csapidus/7971-dustoff-display/photos/IMG_0771.JPG

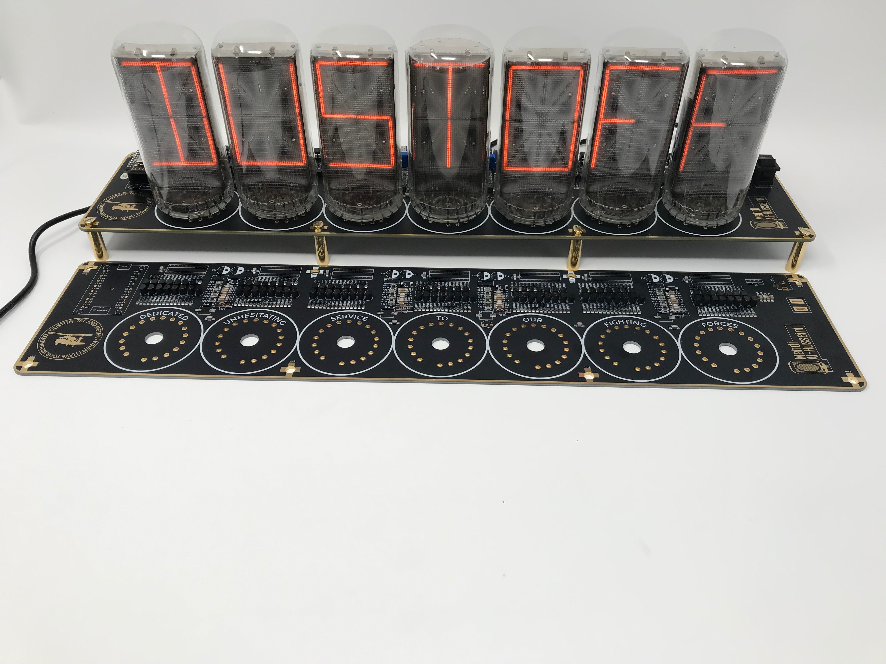
photos/IMG_0771.JPG
