csapidus/7971-dustoff-display/PCB/7971-MEDEVAC-F_SilkS.pdf

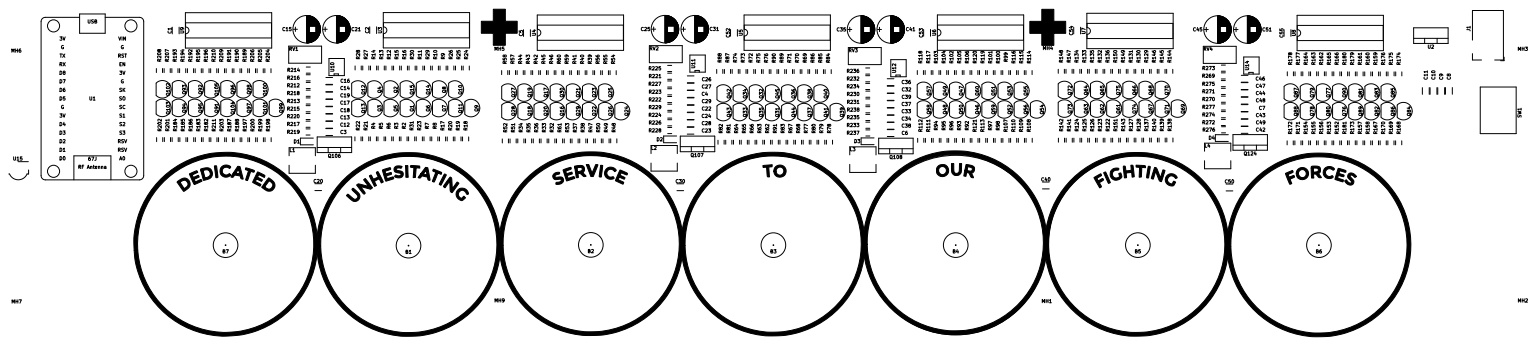
[picture p19: page 1]
